BoujeeEnjinia1701/binlevel/cad/drawings/BNL-DWG-101.pdf

### BUILD PLAN SKETCH, PLAN NOT YET BUILT BinLevel · github.com/BoujeeEnjinia1701/binlevel

FRONT VIEW
Scale 1:2; looking at the front (along +Y)

TOP VIEW
Scale 1:2; looking down (along -Z)

RIGHT VIEW
Scale 1:2; looking at the right side (along -X)

150

80 12

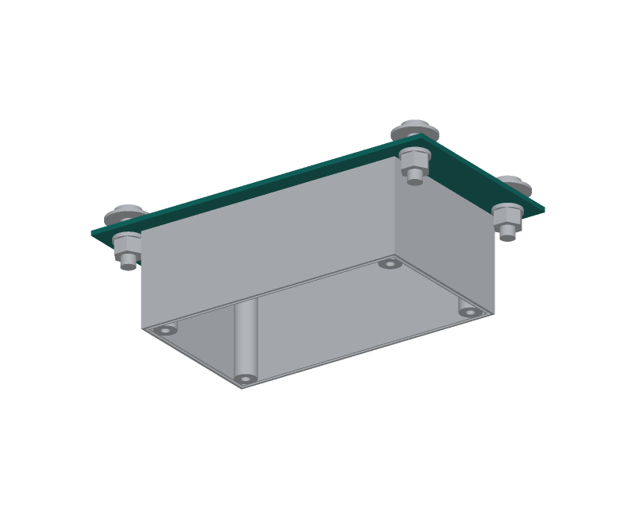
[picture p8: figure]

WHERE IT GOES
This part in colour, its neighbours in grey

HOW TO MAKE IT AND HOW IT FITS
Blank 150 x 80 mm, 2 mm 5052 aluminium, square. Round the corners about 3 mm and deburr every edge.
Measure from the centre lines. The face that goes against the bin
lid is the top face; the box hangs under the other face.
Bolt holes: four 6.6 mm at 65 mm each side of the long centre line and 30 mm each side of the short one (130 x 60).
Stud holes: four 4.2 mm at 40 mm and 18 mm each side
(80 x 36). Check the hole size on the stud maker's sheet.
Press the four M4 x 12 flush-head studs in from the top face with a press or a vice with smooth jaws, until the heads sit flush.
Fit: top face flat on the lid underside; the box base sits flat
on the lower face, the studs through its floor.
Check: studs square to the plate, heads flush, none turns by hand. Finish: prototype, none. Deployments: anodise before pressing in the studs.
REV | DESCRIPTION | DATE | BY
P1 | Making sketch for the prototype build plan | 2026-09-30 | AC
P2 | Finish note added (decided 2026-10-02) | 2026-10-02 | AC
BINLEVEL | github.com/BoujeeEnjinia1701/binlevel

## BinLevel bracket plate: making sketch

DRAWING NO.
BNL-DWG-101

REV
P2

SHEET
1 of 1

SIZE

## ANSI B

SCALE
1:2

UNITS
mm
PROJECTION | DATE
2026-10-02

DRAWN
Amish Chadha

MATERIAL / NOTES
Aluminium sheet 2 mm, 5052 class; four M4 x 12 flush-head press-in studs
Licensed CERN-OHL-S-2.0 · Design Molecule Lab · designmolecule.com | Generated from cad/src; do not edit by hand
