BoujeeEnjinia1701/binlevel/cad/drawings/BNL-DWG-102.pdf

### BUILD PLAN SKETCH, PLAN NOT YET BUILT BinLevel · github.com/BoujeeEnjinia1701/binlevel

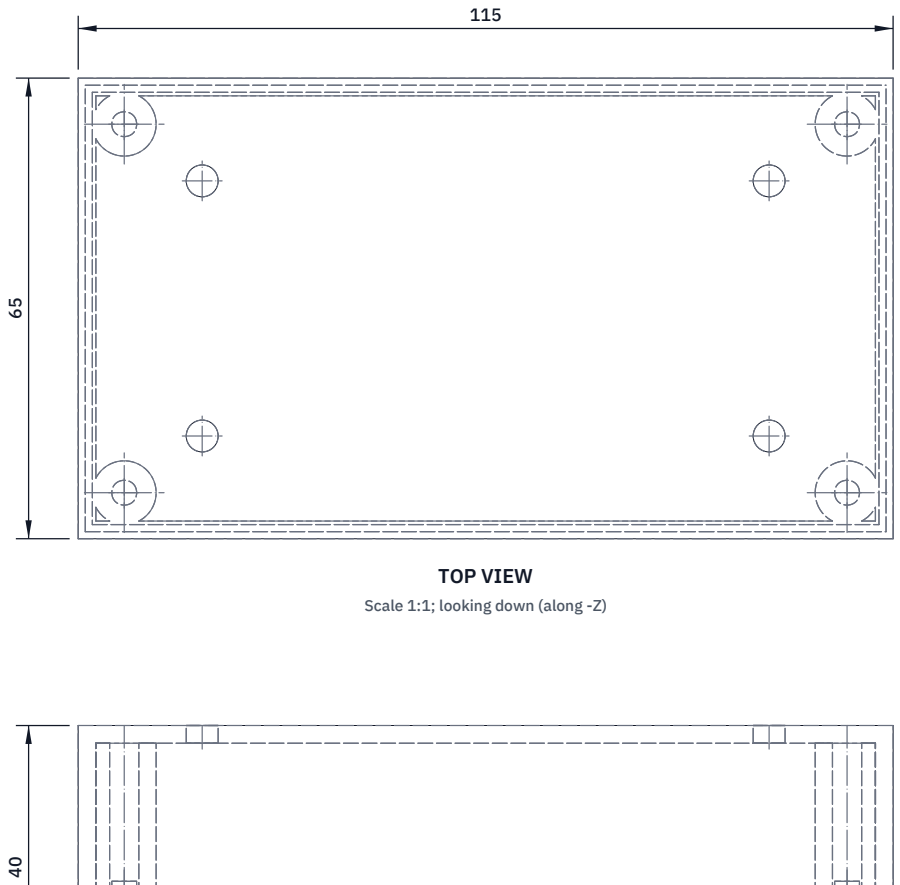
[picture p40: figure]
TOP VIEW; Scale 1:1; looking down (along -Z)
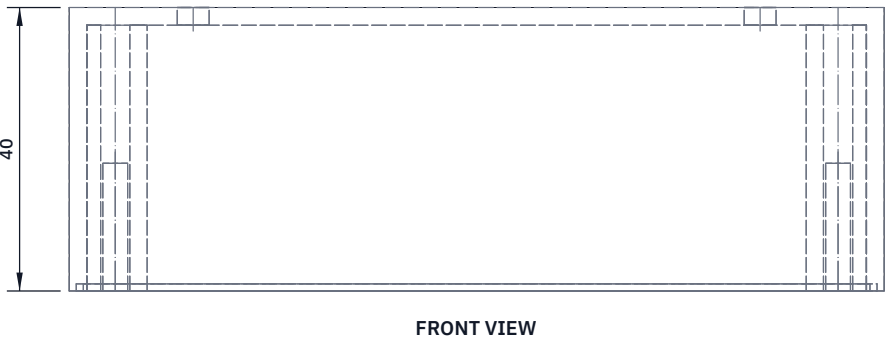
[picture p41: figure]
FRONT VIEW

Scale 1:1; looking at the front (along +Y)

RIGHT VIEW
Scale 1:1; looking at the right side (along -X)

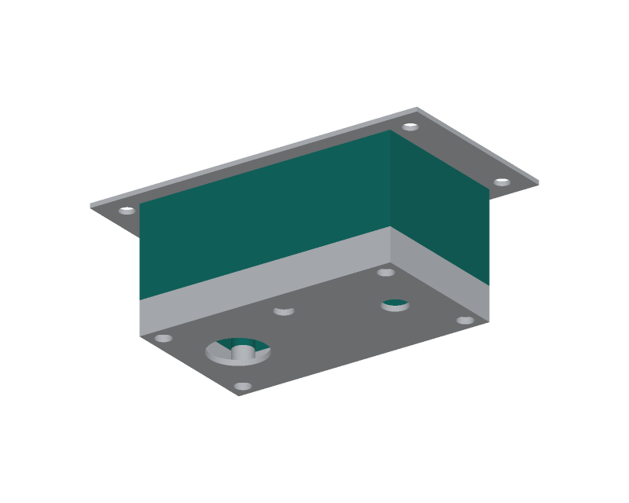
[picture p42: figure]

WHERE IT GOES
This part in colour, its neighbours in grey

HOW TO MAKE IT AND HOW IT FITS
The deep part of a stock IP67 box, 115 x 65 mm outside, 40 mm deep from the rim, 2.5 mm wall, four corner screw towers. Drill four 4.5 mm holes in the floor at 40 and 18 mm each side of the centre lines. Easiest: stand the base on the bracket plate, centre it, and mark through the stud positions.
Tape the floor, pilot drill 2.5 mm slowly with wood behind, then 4.5 mm. Deburr inside and out; no solvents on ABS or PC.
Fit: the outside of the floor sits flat on the plate; the studs pass through, and a sealing washer and a standoff go on each one inside. Check: the base sits flat on the plate with all four studs through and no hole cracked.
REV | DESCRIPTION | DATE | BY
P1 | Making sketch for the prototype build plan | 2026-09-30 | AC
BINLEVEL | github.com/BoujeeEnjinia1701/binlevel

## BinLevel enclosure base: drilling sketch

DRAWING NO.
BNL-DWG-102

REV
P1

SHEET
1 of 1

SIZE

## ANSI B

SCALE
1:1

UNITS
mm
PROJECTION | DATE
2026-09-30

DRAWN
Amish Chadha

MATERIAL / NOTES
Bought IP67 ABS or PC box 115 x 65 x 55 mm (base part)
Licensed CERN-OHL-S-2.0 · Design Molecule Lab · designmolecule.com | Generated from cad/src; do not edit by hand
