BoujeeEnjinia1701/binlevel/cad/drawings/BNL-DWG-103.pdf

### BUILD PLAN SKETCH, PLAN NOT YET BUILT BinLevel · github.com/BoujeeEnjinia1701/binlevel

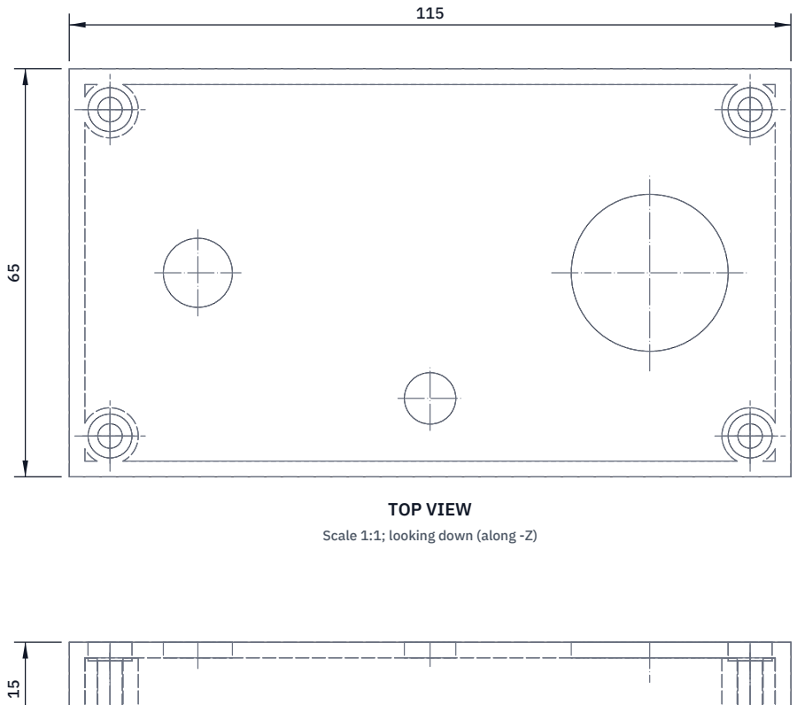
[picture p43: figure]
TOP VIEW; Scale 1:1; looking down (along -Z)

FRONT VIEW
Scale 1:1; looking at the front (along +Y)

RIGHT VIEW
Scale 1:1; looking at the right side (along -X)

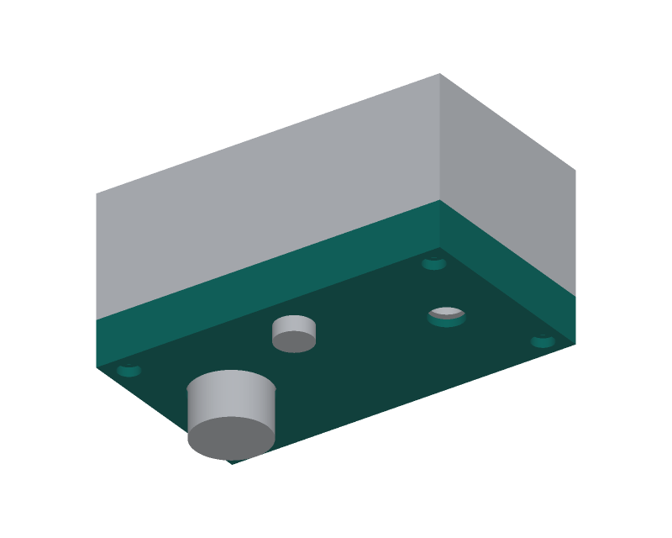
[picture p44: figure]

WHERE IT GOES
This part in colour, its neighbours in grey

HOW TO MAKE IT AND HOW IT FITS
Drawn upside down: the cover lies outside face up with the unit's front edge toward you, as in the cover layout picture of the plan, so the transducer hole is on the right of the top view.
Transducer hole 25 mm, 35 mm from the centre toward the end
that is on the left when the unit is seen from the front. Window
hole 11 mm, 37 mm toward the other end. Both on the long centre line. Vent hole 8.2 mm, on the short centre line, 20 mm from the
long centre line toward the front edge.
Tape the face, pilot 3 mm slowly with wood behind, open out with a step drill, light pressure. Deburr; no solvents.
Fit: the probe goes through the 25 mm hole; the printed collar and ToF holder are bonded inside; the vent nut goes inside.
Check: no crack from any hole under a bright lamp.
REV | DESCRIPTION | DATE | BY
P1 | Making sketch for the prototype build plan | 2026-09-30 | AC
BINLEVEL | github.com/BoujeeEnjinia1701/binlevel

## BinLevel enclosure cover: drilling sketch

DRAWING NO.
BNL-DWG-103

REV
P1

SHEET
1 of 1

SIZE

## ANSI B

SCALE
1:1

UNITS
mm
PROJECTION | DATE
2026-09-30

DRAWN
Amish Chadha

MATERIAL / NOTES
Bought IP67 ABS or PC box 115 x 65 x 55 mm (cover part)
Licensed CERN-OHL-S-2.0 · Design Molecule Lab · designmolecule.com | Generated from cad/src; do not edit by hand
