BoujeeEnjinia1701/binlevel/cad/drawings/BNL-DWG-104.pdf

### BUILD PLAN SKETCH, PLAN NOT YET BUILT BinLevel · github.com/BoujeeEnjinia1701/binlevel

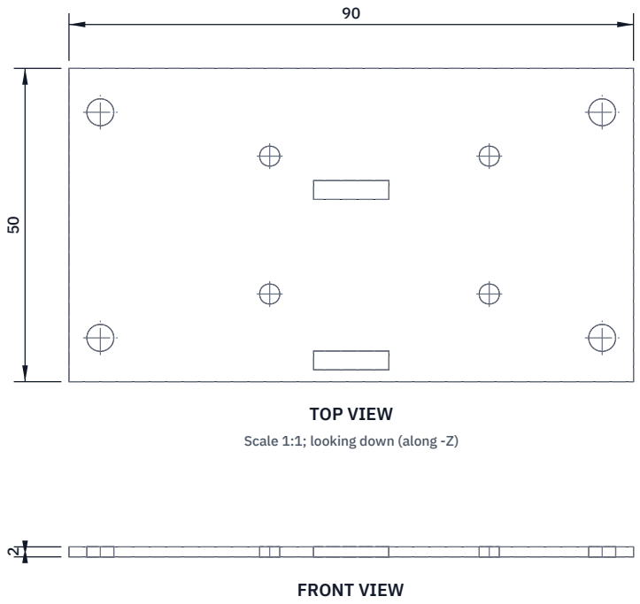
[picture p45: figure]
FRONT VIEW; TOP VIEW; Scale 1:1; looking down (along -Z)

Scale 1:1; looking at the front (along +Y)

RIGHT VIEW
Scale 1:1; looking at the right side (along -X)

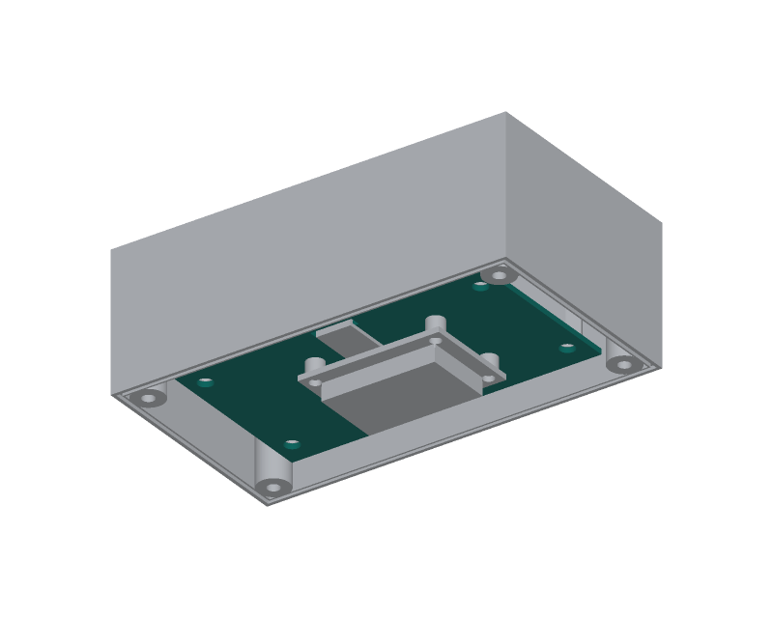
[picture p46: figure]

WHERE IT GOES
This part in colour, its neighbours in grey

HOW TO MAKE IT AND HOW IT FITS
Cut the board to 90 x 50 mm with a fine saw; file the edges smooth. Measure from the centre lines. The top face carries the cell and the breakouts; the driver board hangs under the other face.
Fixing holes: four 4.3 mm at 40 and 18 mm each side of centre. Driver board holes: four 3.2 mm at -13 and 22 mm
along, 11 mm each side across. Match your driver board's holes. Strap slots: two 12 x 3 mm on the cross line, 5.6 mm toward the back edge and 21.6 mm toward the front edge. Drill and file.
Lay out on the top: cell holder along the front half; module,
sensor breakouts, power parts and capacitor along the back half. Fit: the top face sits on the four standoff ends, held by four M4 screws from below.
Check: the board drops onto the standoffs without forcing.
REV | DESCRIPTION | DATE | BY
P1 | Making sketch for the prototype build plan | 2026-09-30 | AC
BINLEVEL | github.com/BoujeeEnjinia1701/binlevel

## BinLevel electronics board: making sketch

DRAWING NO.
BNL-DWG-104

REV
P1

SHEET
1 of 1

SIZE

## ANSI B

SCALE
1:1

UNITS
mm
PROJECTION | DATE
2026-09-30

DRAWN
Amish Chadha

MATERIAL / NOTES
Perforated prototyping board, FR-4, 1.6 mm, 2.54 mm pitch
Licensed CERN-OHL-S-2.0 · Design Molecule Lab · designmolecule.com | Generated from cad/src; do not edit by hand
