BoujeeEnjinia1701/binlevel/cad/drawings/BNL-DWG-105.pdf

### BUILD PLAN SKETCH, PLAN NOT YET BUILT BinLevel · github.com/BoujeeEnjinia1701/binlevel

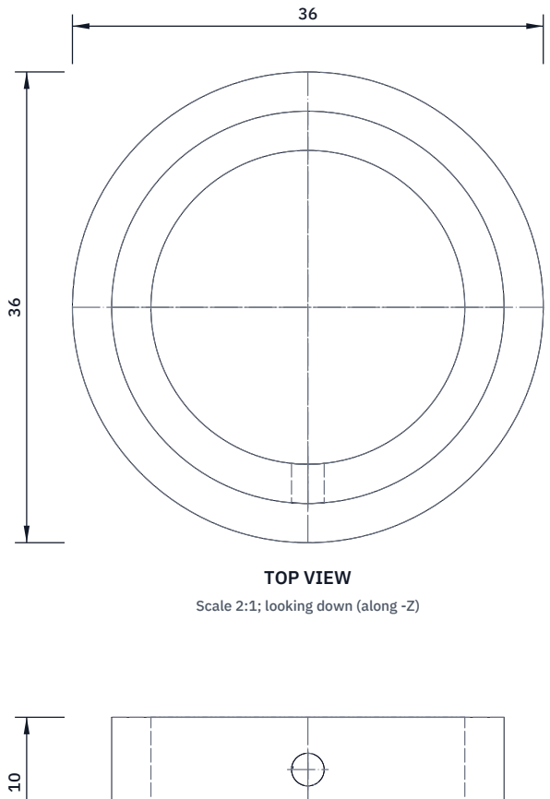
[picture p47: figure]
TOP VIEW; Scale 2:1; looking down (along -Z)

FRONT VIEW
Scale 2:1; looking at the front (along +Y)

RIGHT VIEW
Scale 2:1; looking at the right side (along -X)

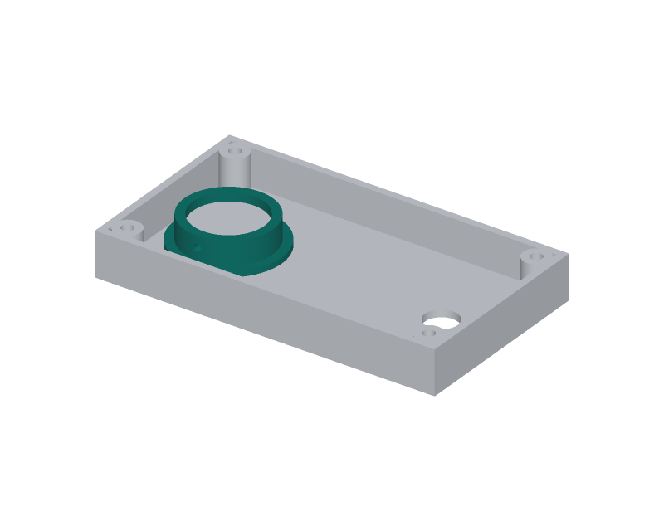
[picture p48: figure]

WHERE IT GOES
This part in colour, its neighbours in grey

HOW TO MAKE IT AND HOW IT FITS
Flange 36 mm across, 2 mm thick; tube 30 mm across,
10 mm tall overall; bore 24.0 mm to suit the probe.
Print flange down in ASA in an enclosed printer. Measure your probe first and print the bore 0.1 to 0.2 mm under it, for a push fit.
Add a 2.5 mm hole through the tube wall 6 mm above the flange and tap it M3 for a nylon-tipped grub screw.
Fit: push the probe through the cover hole from outside so its face stands 14.5 mm proud. Seal the gap in the hole with neutral-cure silicone; slide the collar over the probe from inside and bond the flange to the floor with two-part plastics epoxy.
Tighten the grub screw finger tight once the epoxy has cured. Check: the probe does not move when pushed by hand.
REV | DESCRIPTION | DATE | BY
P1 | Making sketch for the prototype build plan | 2026-09-30 | AC
BINLEVEL | github.com/BoujeeEnjinia1701/binlevel

## BinLevel probe collar: making sketch

DRAWING NO.
BNL-DWG-105

REV
P1

SHEET
1 of 1

SIZE

## ANSI B

SCALE
2:1

UNITS
mm
PROJECTION | DATE
2026-09-30

DRAWN
Amish Chadha

MATERIAL / NOTES
ASA, 3D printed, 100 % infill
Licensed CERN-OHL-S-2.0 · Design Molecule Lab · designmolecule.com | Generated from cad/src; do not edit by hand
