BoujeeEnjinia1701/binlevel/cad/drawings/BNL-DWG-106.pdf

### BUILD PLAN SKETCH, PLAN NOT YET BUILT BinLevel · github.com/BoujeeEnjinia1701/binlevel

FRONT VIEW
Scale 2:1; looking at the front (along +Y)

TOP VIEW
Scale 2:1; looking down (along -Z)

RIGHT VIEW
Scale 2:1; looking at the right side (along -X)

20

22 6

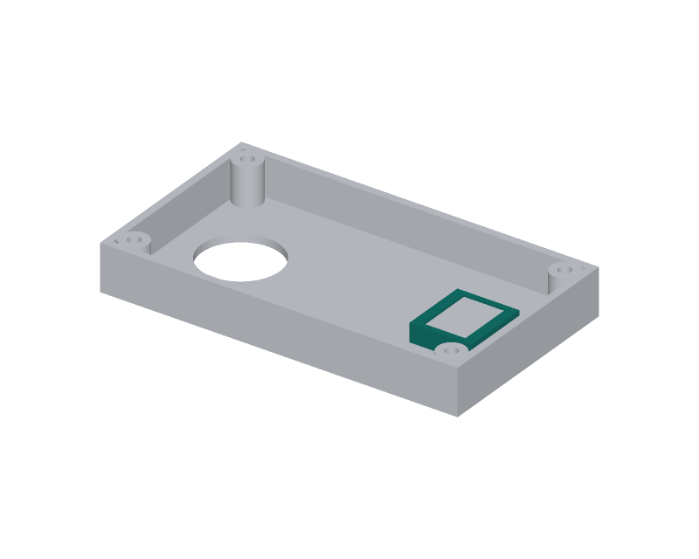
[picture p49: figure]

WHERE IT GOES
This part in colour, its neighbours in grey

HOW TO MAKE IT AND HOW IT FITS
Block 20 x 22 x 6 mm, printed flat in ASA, 100 % infill.
Through it: an 11 mm light hole on its centre.
Underneath: a 16.5 mm recess 1.5 mm deep for the window disc. On top: a 13.5 x 18.5 mm pocket 2 mm deep for the ToF breakout, with two 1.8 mm holes for M2 screws at the breakout's holes. Window: a 16 mm disc of 1.5 mm clear PMMA or glass, cut with a hole saw or bought; keep its film on until fitting.
Fit: window in the recess with a thin ring of neutral-cure silicone on its face; holder centred over the 11 mm cover hole and bonded to the floor with plastics epoxy. Breakout in the pocket, sensor down onto the window, held by two M2 screws.
Check: looking in from outside, the sensor is centred in the hole.
REV | DESCRIPTION | DATE | BY
P1 | Making sketch for the prototype build plan | 2026-09-30 | AC
BINLEVEL | github.com/BoujeeEnjinia1701/binlevel

## BinLevel ToF holder and window: making sketch

DRAWING NO.
BNL-DWG-106

REV
P1

SHEET
1 of 1

SIZE

## ANSI B

SCALE
2:1

UNITS
mm
PROJECTION | DATE
2026-09-30

DRAWN
Amish Chadha

MATERIAL / NOTES
ASA, 3D printed; window 16 mm x 1.5 mm PMMA or glass
Licensed CERN-OHL-S-2.0 · Design Molecule Lab · designmolecule.com | Generated from cad/src; do not edit by hand
