BoujeeEnjinia1701/binlevel/cad/drawings/BNL-DWG-001.png

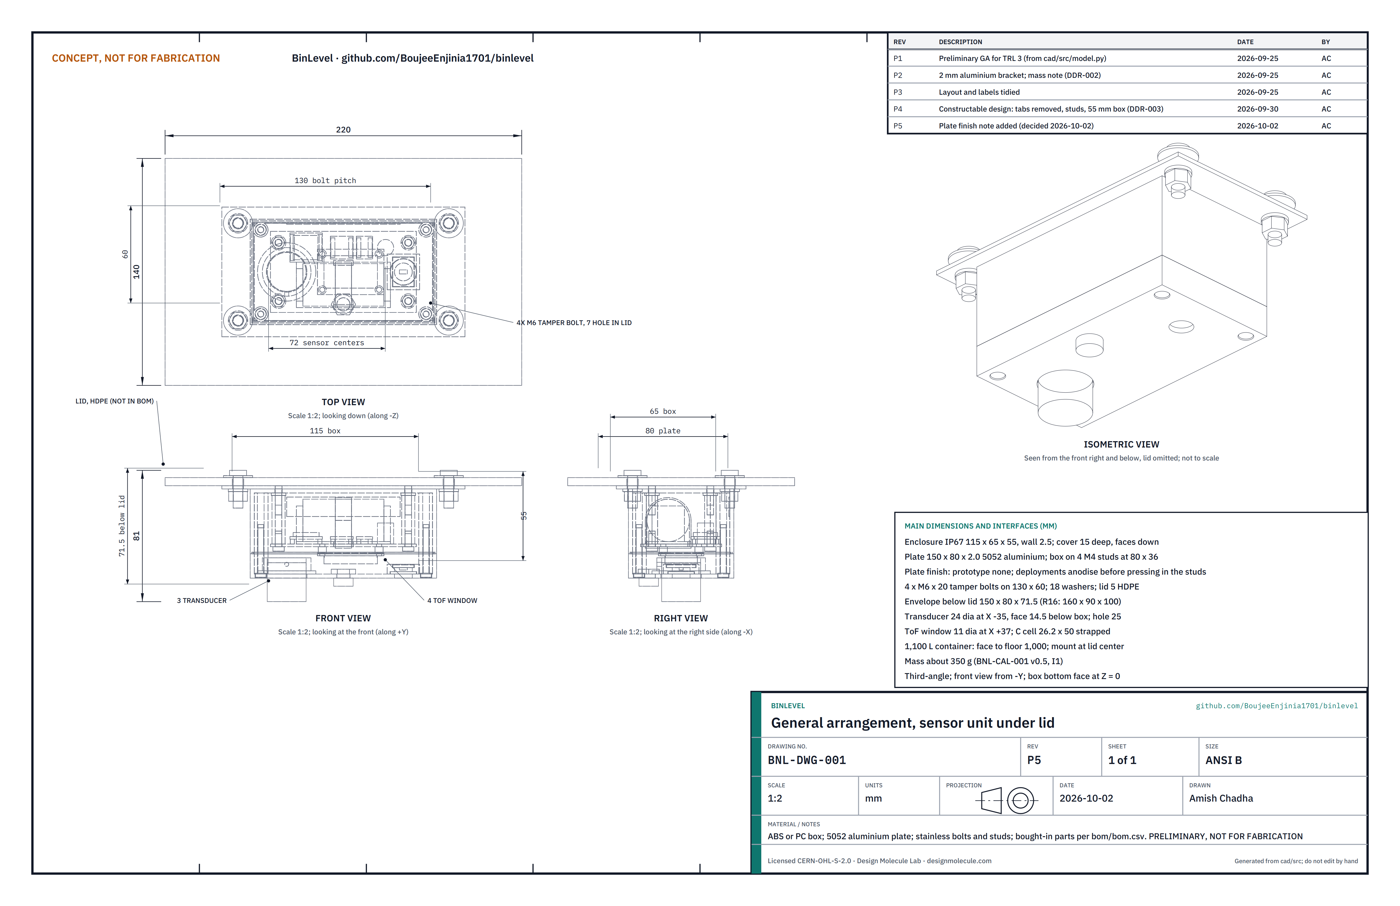
cad/drawings/BNL-DWG-001.png
