BoujeeEnjinia1701/binlevel/media/card.png

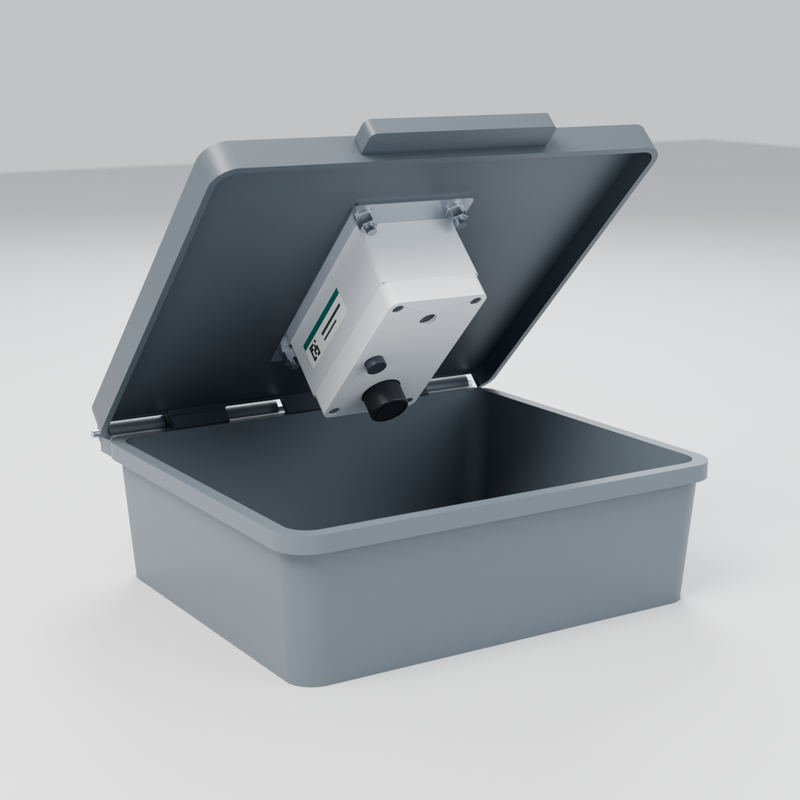
media/card.png
