BoujeeEnjinia1701/binlevel/media/render-detail.png

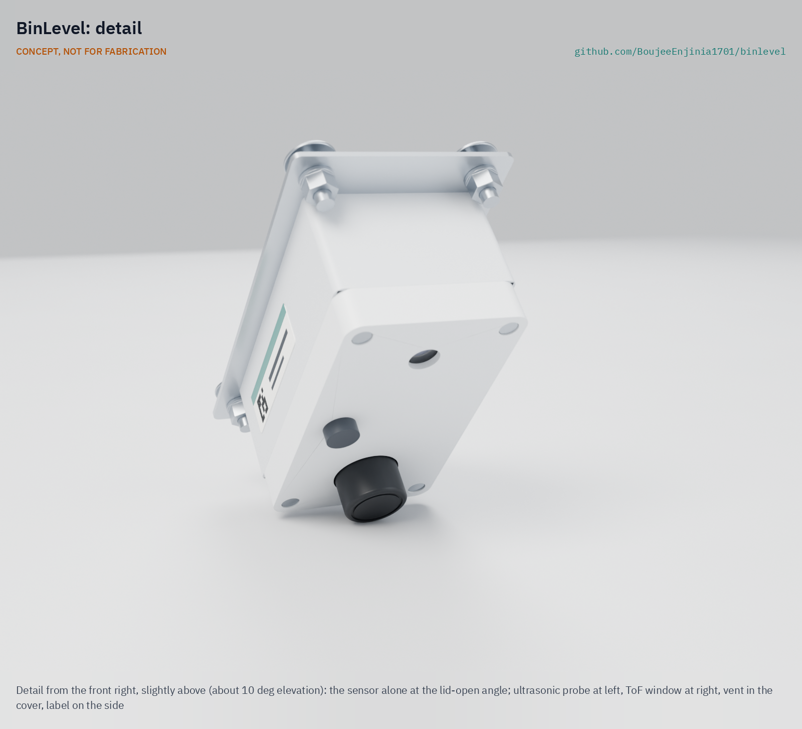
media/render-detail.png
