BoujeeEnjinia1701/binlevel/media/render-exploded.png

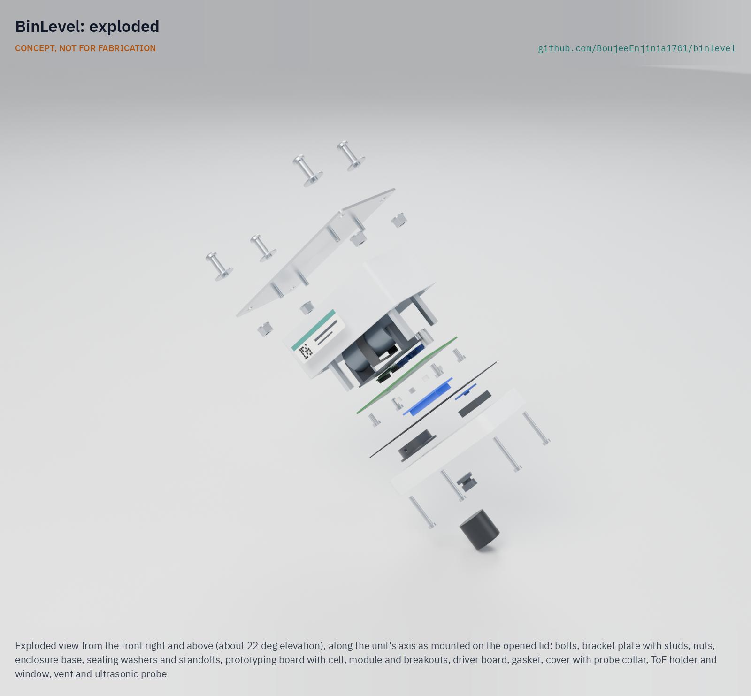
media/render-exploded.png
