BoujeeEnjinia1701/binlevel/media/social-preview.png

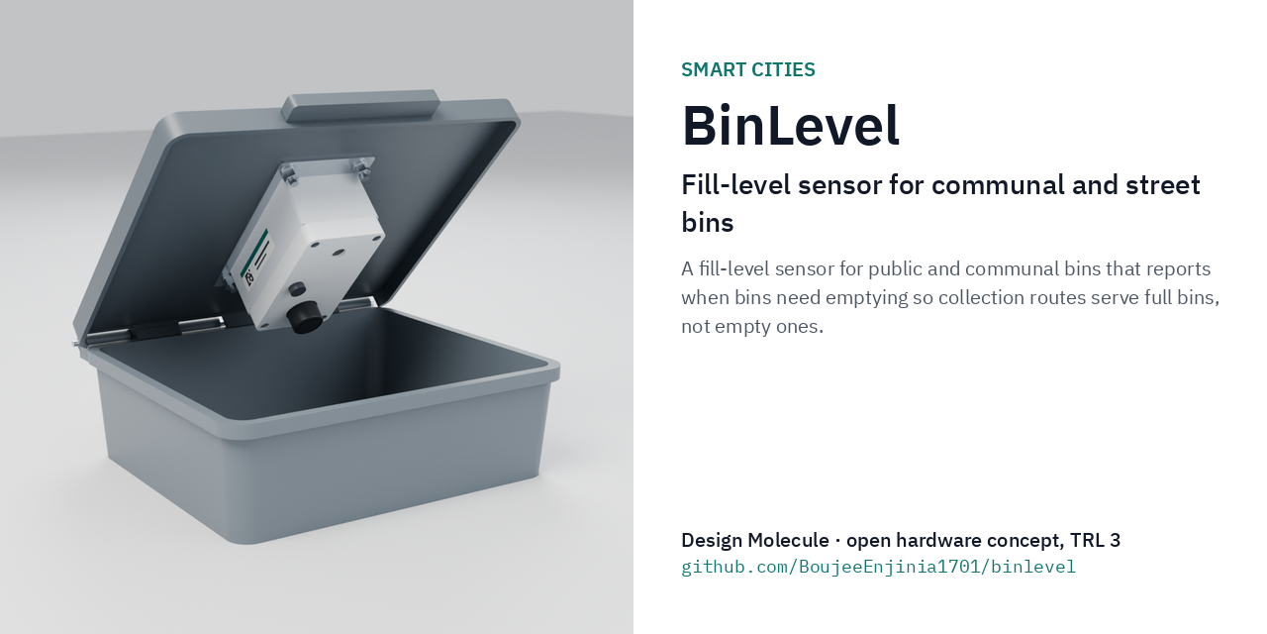
media/social-preview.png
